tlhosep/distance_alarm/freecad/HC-SR04 Housing - 2502264/images/IMG_5308.JPG

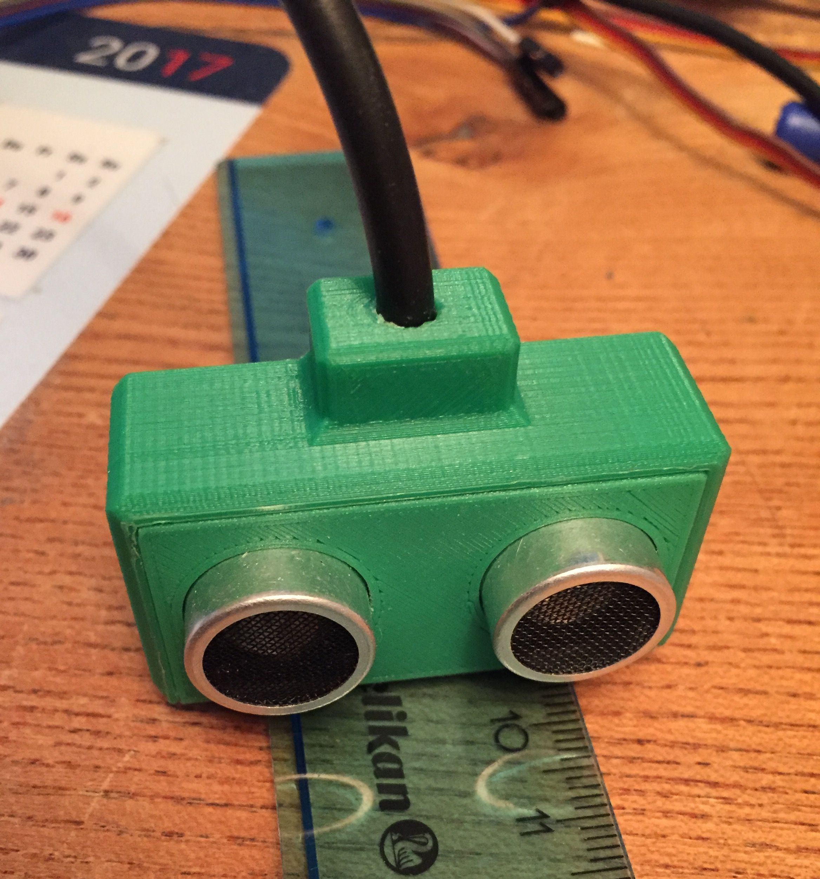
freecad/HC-SR04 Housing - 2502264/images/IMG_5308.JPG
